ptrbroz/Multimeter_watch/Platformio/include/keyboardTest.h

#include "Arduino.h"

funRetVal keyboardTest_init(uint8_t *memPtr);
funRetVal keyboardTest_loop( uint8_t *memPtr);
funRetVal keyboardTest_deinit(uint8_t *memPtr);
extern const program prog_KeyboardTest;
